sprintersb/thermidity/thermidity-avr/bitmaps.c

/*
 * File:   bitmaps.c
 * Author: torsten.roemer@luniks.net
 *
 * Created on 16. April 2023, 18:19
 */

#include <stdio.h>
#include "bitmaps.h"
#include "utils.h"

const __flash uint8_t BAT_0PCT_DATA[] = {
    0x00, 0x00, 0x00, 0x00, 0x00, 0x00, 0x00, 0x00, 
    0x3f, 0xff, 0xff, 0xf0, 0x3f, 0xff, 0xff, 0xf0,
    0x30, 0x00, 0x00, 0x30, 0x30, 0x00, 0x00, 0x30, 
    0x30, 0x00, 0x00, 0x3c, 0x30, 0x00, 0x00, 0x3c,
    0x30, 0x00, 0x00, 0x3c, 0x30, 0x00, 0x00, 0x3c, 
    0x30, 0x00, 0x00, 0x30, 0x30, 0x00, 0x00, 0x30,
    0x3f, 0xff, 0xff, 0xf0, 0x3f, 0xff, 0xff, 0xf0, 
    0x00, 0x00, 0x00, 0x00, 0x00, 0x00, 0x00, 0x00
};

const __flash uint8_t BAT_13PCT_DATA[] = {
    0x00, 0x00, 0x00, 0x00, 0x00, 0x00, 0x00, 0x00, 
    0x3f, 0xff, 0xff, 0xf0, 0x3f, 0xff, 0xff, 0xf0,
    0x3c, 0x00, 0x00, 0x30, 0x3c, 0x00, 0x00, 0x30, 
    0x3c, 0x00, 0x00, 0x3c, 0x3c, 0x00, 0x00, 0x3c,
    0x3c, 0x00, 0x00, 0x3c, 0x3c, 0x00, 0x00, 0x3c, 
    0x3c, 0x00, 0x00, 0x30, 0x3c, 0x00, 0x00, 0x30,
    0x3f, 0xff, 0xff, 0xf0, 0x3f, 0xff, 0xff, 0xf0, 
    0x00, 0x00, 0x00, 0x00, 0x00, 0x00, 0x00, 0x00
};

const __flash uint8_t BAT_25PCT_DATA[] = {
    0x00, 0x00, 0x00, 0x00, 0x00, 0x00, 0x00, 0x00, 
    0x3f, 0xff, 0xff, 0xf0, 0x3f, 0xff, 0xff, 0xf0,
    0x3f, 0x80, 0x00, 0x30, 0x3f, 0x80, 0x00, 0x30, 
    0x3f, 0x80, 0x00, 0x3c, 0x3f, 0x80, 0x00, 0x3c,
    0x3f, 0x80, 0x00, 0x3c, 0x3f, 0x80, 0x00, 0x3c, 
    0x3f, 0x80, 0x00, 0x30, 0x3f, 0x80, 0x00, 0x30,
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
    {32, 16, BAT_0PCT_DATA},
    {32, 16, BAT_13PCT_DATA},
    {32, 16, BAT_25PCT_DATA},
    {32, 16, BAT_38PCT_DATA},
    {32, 16, BAT_50PCT_DATA},
    {32, 16, BAT_63PCT_DATA},
    {32, 16, BAT_75PCT_DATA},
    {32, 16, BAT_88PCT_DATA},
    {32, 16, BAT_100PCT_DATA}
};
