sprintersb/thermidity/thermidity-avr/sram.c

/* 
 * File:   sram.c
 * Author: torsten.roemer@luniks.net
 *
 * Created on 1. April 2023, 18:59
 */

#include <stdlib.h>
#include <stdio.h>
#include <string.h>
#include "sram.h"
#include "spi.h"

void sramWrite(uint16_t address, uint8_t data) {
    sramSel();
    transmit(SRAM_WRITE);
    transmit(address >> 8);
    transmit(address);
    transmit(data);
    sramDes();
}

size_t sramWriteString(uint16_t address, const char *data) {
    size_t written = 0;
    for (; address <= SRAM_HIGH; ++address) {
        char c = *data++;
        if (c == 0) {
            break;
        }
        sramWrite(address, c);
        written++;
    }
    
    return written;
}

uint8_t sramRead(uint16_t address) {
    sramSel();
    transmit(SRAM_READ);
    transmit(address >> 8);
    transmit(address);
    uint8_t read = transmit(0);
    sramDes();

    return read;
}

void sramReadString(uint16_t address, char *buf, size_t length) {
    for (size_t i = 0; i < length - 1; i++) {
        if (address > SRAM_HIGH) {
            break;
        }
        buf[i] = sramRead(address++);
    }
    buf[length - 1] = '\0';
}

void sramWriteStatus(uint8_t status) {
    sramSel();
    transmit(SRAM_WRSR);
    transmit(status);
    sramDes();
}

uint8_t sramReadStatus(void) {
    sramSel();
    transmit(SRAM_RDSR);
    uint8_t status = transmit(0);
    sramDes();

    return status;
}

void sramInitWrite(uint16_t address) {
    transmit(SRAM_WRITE);
    transmit(address >> 8);
    transmit(address);    
}

void sramInitRead(uint16_t address) {
    transmit(SRAM_READ);
    transmit(address >> 8);
    transmit(address);    
}
